klad-me/RK8266/pcb/ESP-01-LUT/mount/back.png

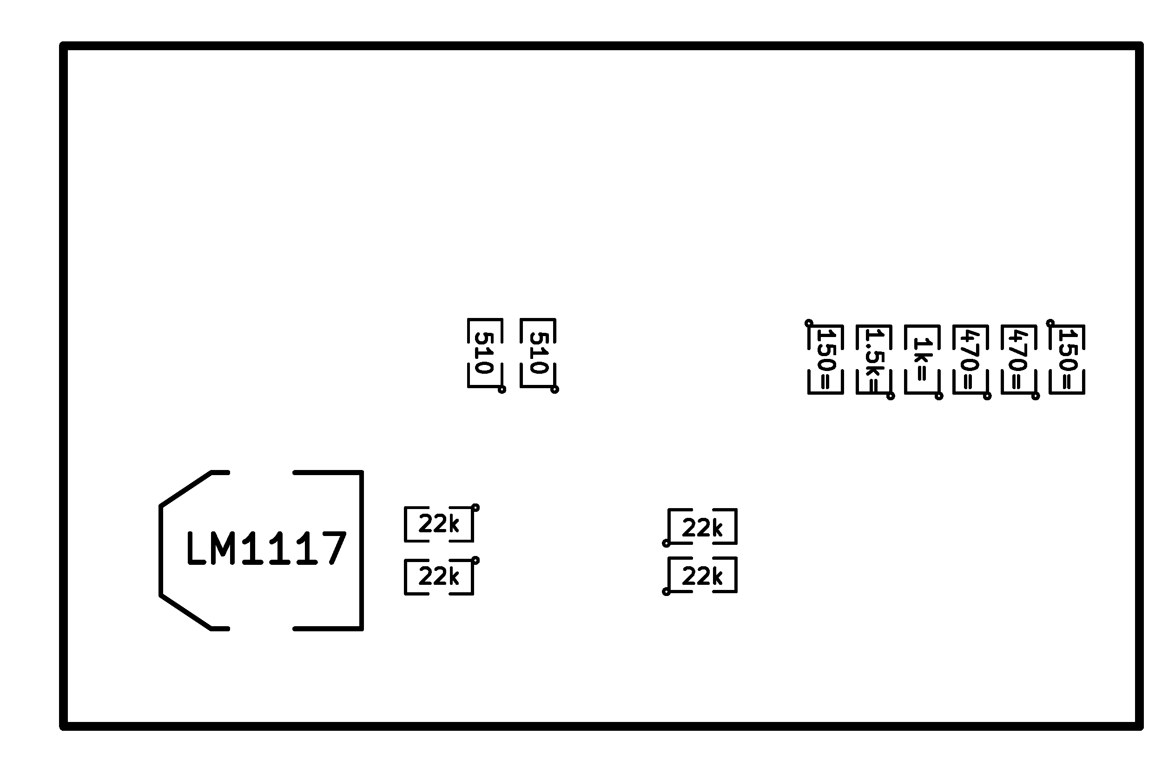
pcb/ESP-01-LUT/mount/back.png
