klad-me/RK8266/pcb/ESP-01-LUT/mount/front.png

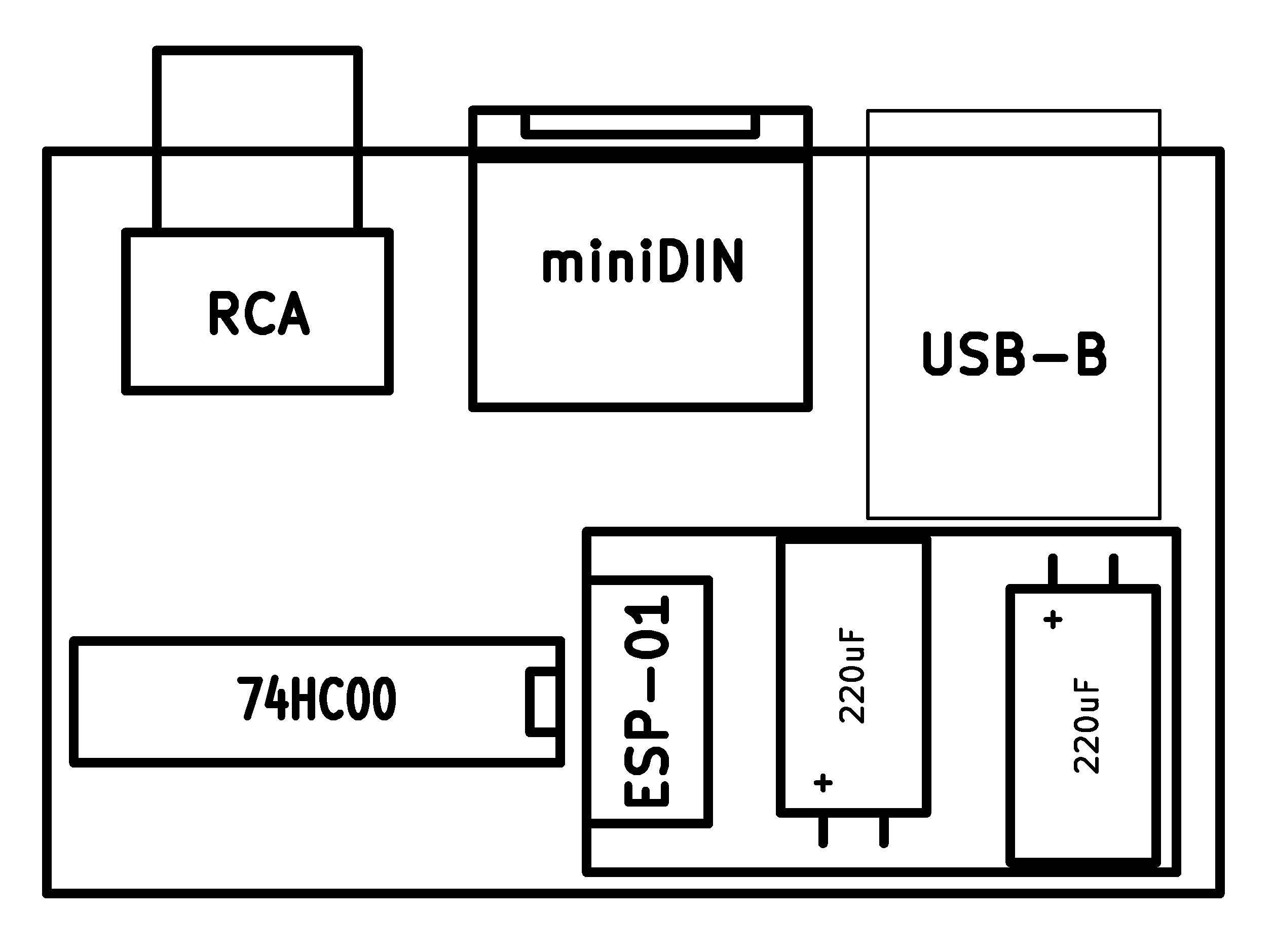
pcb/ESP-01-LUT/mount/front.png
