klad-me/RK8266/screenshots/rk8266_1.png

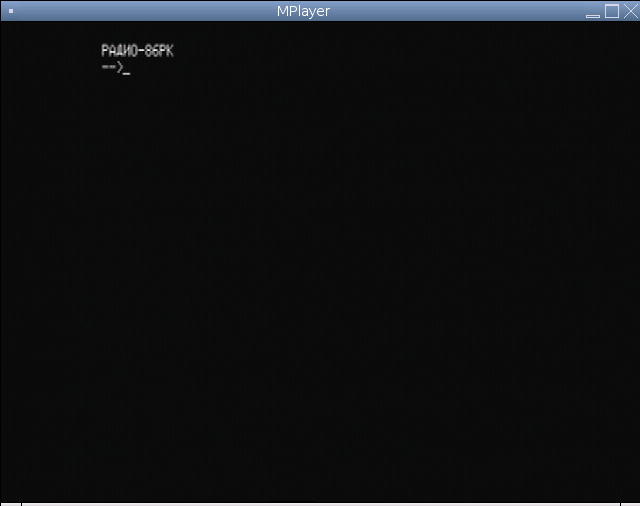
screenshots/rk8266_1.png
