klad-me/RK8266/screenshots/rk8266_3.png

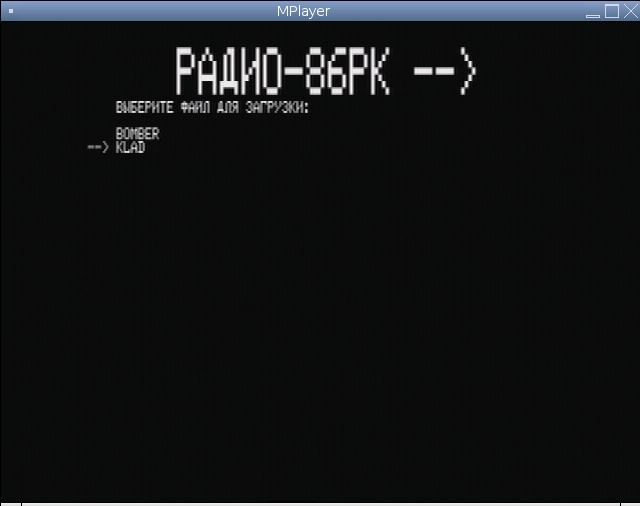
screenshots/rk8266_3.png
