klad-me/RK8266/screenshots/rk8266_4.png

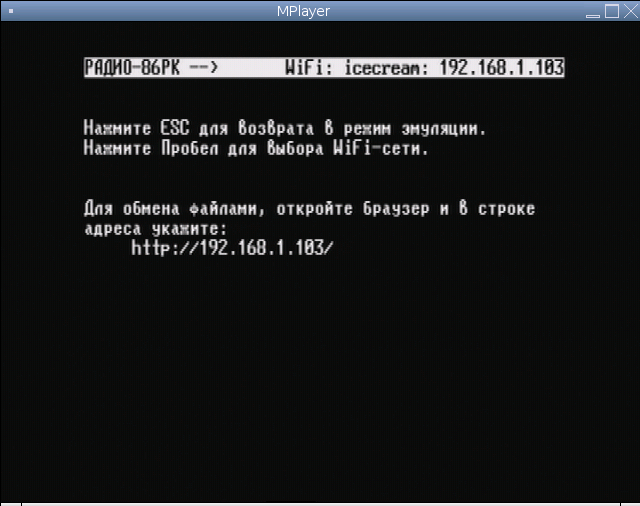
screenshots/rk8266_4.png
