klad-me/RK8266/screenshots/rk8266_5.png

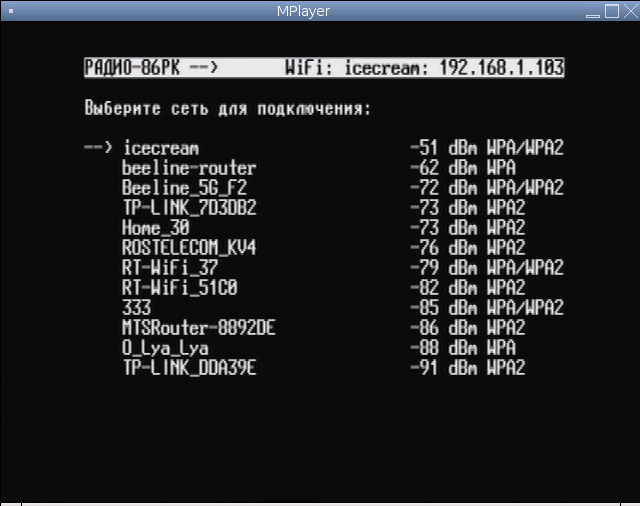
screenshots/rk8266_5.png
