klad-me/RK8266/screenshots/rk8266_7.png

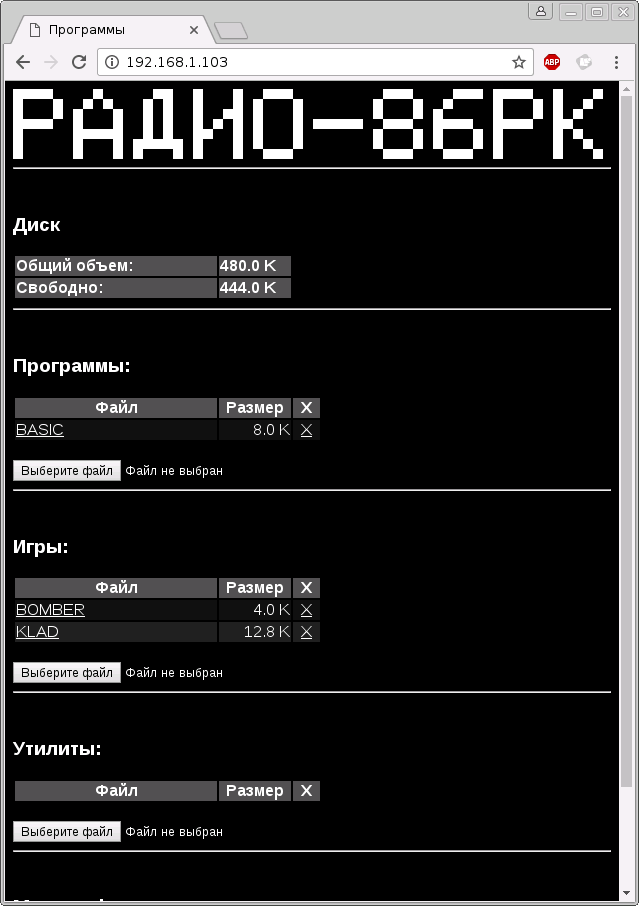
screenshots/rk8266_7.png
