klad-me/RK8266/pcb/ESP-01-LUT/RK86.sch

## KiCad design pcb/ESP-01-LUT/RK86.sch (2018-03-06)

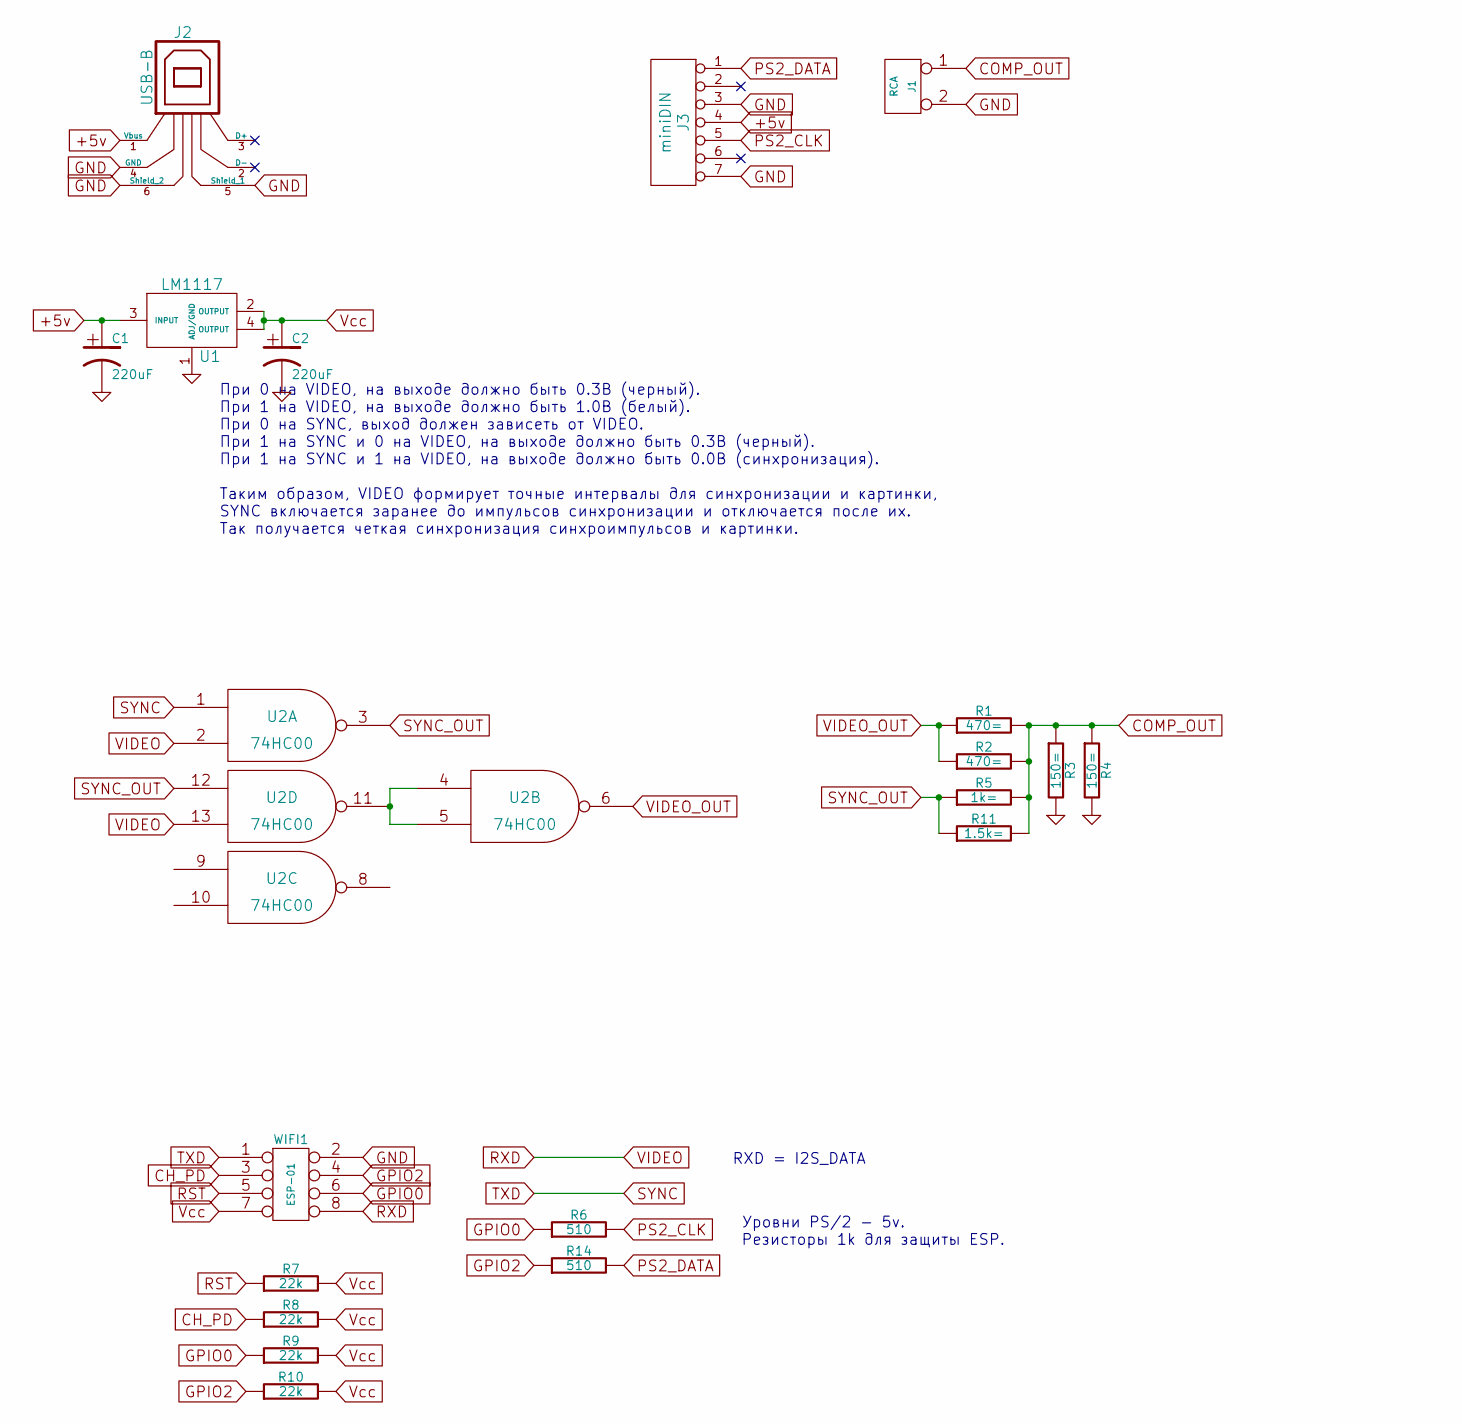
[picture p16: schematic RK86.sch]

Parts:
C1, C2: 220uF
J1: RCA
J2: USB-B
J3: miniDIN
R1, R2: 470=
R3, R4: 150=
R5: 1k=
R6, R14: 510
R7, R8, R9, R10: 22k
R11: 1.5k=
U1: LM1117
U2: 74HC00
WIFI1: ESP-01

Connections:
+5v: C1.1, J2.1 (Vbus), J3.4, U1.3 (INPUT)
CH_PD: R8.1, WIFI1.3
COMP_OUT: J1.1, R1.2, R2.2, R3.1, R4.1, R5.2, R11.2
GND: C1.2, C2.2, J1.2 (PM), J2.4 (GND), J2.5 (Shield_1), J2.6 (Shield_2), J3.3, J3.7, R3.2, R4.2, U1.1 (ADJ/GND), WIFI1.2
GPIO0: R6.1, R9.1, WIFI1.6
GPIO2: R10.1, R14.1, WIFI1.4
unnamed: U2.4, U2.5, U2.11
PS2_CLK: J3.5, R6.2
PS2_DATA: J3.1, R14.2
RST: R7.1, WIFI1.5
RXD: U2.2, U2.13, WIFI1.8
SYNC: U2.1, WIFI1.1
SYNC_OUT: R5.1, R11.1, U2.3, U2.12
VIDEO_OUT: R1.1, R2.1, U2.6
Vcc: C2.1, R7.2, R8.2, R9.2, R10.2, U1.2 (OUTPUT), U1.4 (OUTPUT), WIFI1.7

Notes on the sheet:
Уровни PS/2 - 5v. Резисторы 1k для защиты ESP.
RXD = I2S_DATA
При 0 на VIDEO, на выходе должно быть 0.3В (черный). При 1 на VIDEO, на выходе должно быть 1.0В (белый). При 0 на SYNC, выход должен зависеть от VIDEO. При 1 на SYNC и 0 на VIDEO, на выходе должно быть 0.3В (черный). При 1 на SYNC и 1 на VIDEO, на выходе должно быть 0.0В (синхронизация). Таким обра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
