klad-me/RK8266/soft/EmuAPP/src/rom.h

static const unsigned char AT_IRAM ROM_F800[] = {
  0xc3, 0x36, 0xf8, 0xc3, 0x63, 0xfe, 0xc3, 0x98, 0xfb, 0xc3, 0xba, 0xfc,
  0xc3, 0x46, 0xfc, 0xc3, 0xba, 0xfc, 0xc3, 0x01, 0xfe, 0xc3, 0xa5, 0xfc,
  0xc3, 0x22, 0xf9, 0xc3, 0x72, 0xfe, 0xc3, 0x7b, 0xfa, 0xc3, 0x7f, 0xfa,
  0xc3, 0xb6, 0xfa, 0xc3, 0x49, 0xfb, 0xc3, 0x16, 0xfb, 0xc3, 0xce, 0xfa,
  0xc3, 0x52, 0xff, 0xc3, 0x56, 0xff, 0x3e, 0x8a, 0x32, 0x03, 0x80, 0x31,
  0xcf, 0x76, 0xcd, 0xce, 0xfa, 0x21, 0x00, 0x76, 0x11, 0x5f, 0x76, 0x0e,
  0x00, 0xcd, 0xed, 0xf9, 0x21, 0xcf, 0x76, 0x22, 0x1c, 0x76, 0x21, 0x5a,
  0xff, 0xcd, 0x22, 0xf9, 0xcd, 0xce, 0xfa, 0x21, 0xff, 0x75, 0x22, 0x31,
  0x76, 0x21, 0x2a, 0x1d, 0x22, 0x2f, 0x76, 0x3e, 0xc3, 0x32, 0x26, 0x76,
  0x31, 0xcf, 0x76, 0x21, 0x66, 0xff, 0xcd, 0x22, 0xf9, 0x32, 0x02, 0x80,
  0x3d, 0x32, 0x02, 0xa0, 0xcd, 0xee, 0xf8, 0x21, 0x6c, 0xf8, 0xe5, 0x21,
  0x33, 0x76, 0x7e, 0xfe, 0x58, 0xca, 0xd3, 0xff, 0xfe, 0x55, 0xca, 0x00,
  0xf0, 0xf5, 0xcd, 0x2c, 0xf9, 0x2a, 0x2b, 0x76, 0x4d, 0x44, 0x2a, 0x29,
  0x76, 0xeb, 0x2a, 0x27, 0x76, 0xf1, 0xfe, 0x44, 0xca, 0xc5, 0xf9, 0xfe,
  0x43, 0xca, 0xd7, 0xf9, 0xfe, 0x46, 0xca, 0xed, 0xf9, 0xfe, 0x53, 0xca,
  0xf4, 0xf9, 0xfe, 0x54, 0xca, 0xff, 0xf9, 0xfe, 0x4d, 0xca, 0x26, 0xfa,
  0xfe, 0x47, 0xca, 0x3f, 0xfa, 0xfe, 0x49, 0xca, 0x86, 0xfa, 0xfe, 0x4f,
  0xca, 0x2d, 0xfb, 0xfe, 0x4c, 0xca, 0x08, 0xfa, 0xfe, 0x52, 0xca, 0x68,
  0xfa, 0xc3, 0x00, 0xf0, 0x3e, 0x33, 0xbd, 0xca, 0xf1, 0xf8, 0xe5, 0x21,
  0x9e, 0xff, 0xcd, 0x22, 0xf9, 0xe1, 0x2b, 0xc3, 0xf3, 0xf8, 0x21, 0x33,
  0x76, 0x06, 0x00, 0xcd, 0x63, 0xfe, 0xfe, 0x08, 0xca, 0xdc, 0xf8, 0xfe,
  0x7f, 0xca, 0xdc, 0xf8, 0xc4, 0xb9, 0xfc, 0x77, 0xfe, 0x0d, 0xca, 0x1a,
  0xf9, 0xfe, 0x2e, 0xca, 0x6c, 0xf8, 0x06, 0xff, 0x3e, 0x52, 0xbd, 0xca,
  0xae, 0xfa, 0x23, 0xc3, 0xf3, 0xf8, 0x78, 0x17, 0x11, 0x33, 0x76, 0x06,
  0x00, 0xc9, 0x7e, 0xa7, 0xc8, 0xcd, 0xb9, 0xfc, 0x23, 0xc3, 0x22, 0xf9,
  0x21, 0x27, 0x76, 0x11, 0x2d, 0x76, 0x0e, 0x00, 0xcd, 0xed, 0xf9, 0x11,
  0x34, 0x76, 0xcd, 0x5a, 0xf9, 0x22, 0x27, 0x76, 0x22, 0x29, 0x76, 0xd8,
  0x3e, 0xff, 0x32, 0x2d, 0x76, 0xcd, 0x5a, 0xf9, 0x22, 0x29, 0x76, 0xd8,
  0xcd, 0x5a, 0xf9, 0x22, 0x2b, 0x76, 0xd8, 0xc3, 0xae, 0xfa, 0x21, 0x00,
  0x00, 0x1a, 0x13, 0xfe, 0x0d, 0xca, 0x8e, 0xf9, 0xfe, 0x2c, 0xc8, 0xfe,
  0x20, 0xca, 0x5d, 0xf9, 0xd6, 0x30, 0xfa, 0xae, 0xfa, 0xfe, 0x0a, 0xfa,
  0x82, 0xf9, 0xfe, 0x11, 0xfa, 0xae, 0xfa, 0xfe, 0x17, 0xf2, 0xae, 0xfa,
  0xd6, 0x07, 0x4f, 0x29, 0x29, 0x29, 0x29, 0xda, 0xae, 0xfa, 0x09, 0xc3,
  0x5d, 0xf9, 0x37, 0xc9, 0x7c, 0xba, 0xc0, 0x7d, 0xbb, 0xc9, 0xcd, 0xa4,
  0xf9, 0xcd, 0x90, 0xf9, 0xc2, 0xa2, 0xf9, 0x33, 0x33, 0xc9, 0x23, 0xc9,
  0xcd, 0x72, 0xfe, 0xfe, 0x03, 0xc0, 0xcd, 0xce, 0xfa, 0xc3, 0xae, 0xfa,
  0xe5, 0x21, 0x6c, 0xff, 0xcd, 0x22, 0xf9, 0xe1, 0xc9, 0x7e, 0xc5, 0xcd,
  0xa5, 0xfc, 0x3e, 0x20, 0xcd, 0xb9, 0xfc, 0xc1, 0xc9, 0xcd, 0x78, 0xfb,
  0xcd, 0xb9, 0xf9, 0xcd, 0x96, 0xf9, 0x7d, 0xe6, 0x0f, 0xca, 0xc5, 0xf9,
  0xc3, 0xc8, 0xf9, 0x0a, 0xbe, 0xca, 0xe6, 0xf9, 0xcd, 0x78, 0xfb, 0xcd,
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
};
