klad-me/RK8266/soft/EmuAPP/src/zkg.c

#include "zkg.h"

#include "ets.h"


uint8_t zkg[4][1024];

const uint8_t AT_IRAM zkg_rom[1024]=
{
    // Line 0
    0x00, 0x38, 0x07, 0x3f, 0x00, 0x38, 0x07, 0x3f, 0x00, 0x0c, 0x00, 0x0c, 0x00, 0x00, 0x08, 0x0c, 
    0x00, 0x38, 0x07, 0x3f, 0x00, 0x38, 0x07, 0x3f, 0x00, 0x00, 0x00, 0x0c, 0x00, 0x04, 0x03, 0x00, 
    0x00, 0x04, 0x0a, 0x0a, 0x11, 0x18, 0x04, 0x06, 0x02, 0x08, 0x00, 0x00, 0x00, 0x00, 0x00, 0x00, 
    0x0e, 0x04, 0x0e, 0x1f, 0x02, 0x1f, 0x07, 0x1f, 0x0e, 0x0e, 0x00, 0x0c, 0x02, 0x00, 0x08, 0x0e, 
    0x0e, 0x04, 0x1e, 0x0e, 0x1e, 0x1f, 0x1f, 0x0e, 0x11, 0x0e, 0x01, 0x11, 0x10, 0x11, 0x11, 0x0e, 
    0x1e, 0x0e, 0x1e, 0x0e, 0x1f, 0x11, 0x11, 0x11, 0x11, 0x11, 0x1f, 0x0e, 0x00, 0x0e, 0x0e, 0x00, 
    0x12, 0x04, 0x1f, 0x12, 0x06, 0x1f, 0x04, 0x1f, 0x11, 0x11, 0x15, 0x11, 0x07, 0x11, 0x11, 0x0e, 
    0x1f, 0x0f, 0x1e, 0x0e, 0x1f, 0x11, 0x11, 0x1e, 0x10, 0x11, 0x0e, 0x11, 0x0e, 0x15, 0x11, 0x3f, 
    // Line 1
    0x00, 0x38, 0x07, 0x3f, 0x00, 0x38, 0x07, 0x3f, 0x00, 0x0c, 0x00, 0x1e, 0x00, 0x00, 0x0c, 0x0c, 
    0x00, 0x38, 0x07, 0x3f, 0x00, 0x38, 0x07, 0x3f, 0x00, 0x00, 0x00, 0x0c, 0x00, 0x0c, 0x04, 0x00, 
    0x00, 0x04, 0x0a, 0x0a, 0x0e, 0x19, 0x0a, 0x06, 0x04, 0x04, 0x04, 0x04, 0x00, 0x00, 0x00, 0x01, 
    0x11, 0x0c, 0x11, 0x01, 0x06, 0x10, 0x08, 0x01, 0x11, 0x11, 0x0c, 0x0c, 0x04, 0x00, 0x04, 0x11, 
    0x11, 0x0a, 0x11, 0x11, 0x09, 0x10, 0x10, 0x11, 0x11, 0x04, 0x01, 0x12, 0x10, 0x1b, 0x11, 0x11, 
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
    0x11, 0x11, 0x10, 0x0e, 0x04, 0x10, 0x11, 0x1e, 0x1e, 0x19, 0x0e, 0x1f, 0x0e, 0x01, 0x00, 0x3f, 
    // Line 7
    0x00, 0x00, 0x00, 0x00, 0x07, 0x07, 0x07, 0x07, 0x00, 0x21, 0x00, 0x0c, 0x00, 0x00, 0x08, 0x0c, 
    0x38, 0x38, 0x38, 0x38, 0x3f, 0x3f, 0x3f, 0x3f, 0x00, 0x00, 0x00, 0x0c, 0x00, 0x04, 0x0c, 0x00, 
    0x00, 0x00, 0x00, 0x00, 0x00, 0x00, 0x00, 0x00, 0x00, 0x00, 0x00, 0x00, 0x00, 0x00, 0x00, 0x00, 
    0x00, 0x00, 0x00, 0x00, 0x00, 0x00, 0x00, 0x00, 0x00, 0x00, 0x00, 0x00, 0x00, 0x00, 0x00, 0x00, 
    0x00, 0x00, 0x00, 0x00, 0x00, 0x00, 0x00, 0x00, 0x00, 0x00, 0x00, 0x00, 0x00, 0x00, 0x00, 0x00, 
    0x00, 0x00, 0x00, 0x00, 0x00, 0x00, 0x00, 0x00, 0x00, 0x00, 0x00, 0x00, 0x00, 0x00, 0x00, 0x00, 
    0x00, 0x00, 0x00, 0x00, 0x00, 0x00, 0x00, 0x00, 0x00, 0x00, 0x00, 0x00, 0x00, 0x00, 0x00, 0x00, 
    0x00, 0x00, 0x00, 0x00, 0x00, 0x00, 0x00, 0x00, 0x00, 0x00, 0x00, 0x00, 0x00, 0x00, 0x3f, 0x00, 
};
