klad-me/RK8266/soft/EmuAPP/src/tv.h

#ifndef TV_H
#define TV_H


#include "ets.h"


#ifdef __cplusplus
extern "C" {
#endif


extern uint8_t tv_empty_line[64];


void tv_init(void);
void tv_start(void);


#ifdef __cplusplus
}
#endif


#endif
