klad-me/RK8266/soft/EmuAPP/src/align4.h

#ifndef ALIGN4_H
#define ALIGN4_H


#include <inttypes.h>


#ifdef __cplusplus
extern "C" {
#endif


uint8_t  r_u8(const uint8_t *addr);
uint16_t r_u16(const uint16_t *addr);


#ifdef __cplusplus
}
#endif


#endif
