klad-me/RK8266/soft/boot-2apps/src/ram_loader.h

const uint32_t entry_addr = 0x4010fcd4;

const uint32_t _text_addr = 0x4010fc00;
const uint32_t _text_len = 224;
const uint8_t  _text_data[] = {
  0x00, 0x00, 0x00, 0x00, 0x00, 0x00, 0x00, 0x00, 0x00, 0x00, 0x00, 0x00, 0x00, 0x00, 0x00, 0x00,
  0x00, 0x00, 0x00, 0x00, 0x00, 0x00, 0x00, 0x00, 0x00, 0x00, 0x00, 0x00, 0x00, 0x00, 0x00, 0x00,
  0x00, 0x00, 0x00, 0x00, 0x00, 0x00, 0x00, 0x00, 0x00, 0x00, 0x00, 0x00, 0x00, 0x00, 0x00, 0x00,
  0x1c, 0x4b, 0x00, 0x40, 0xb4, 0x18, 0x00, 0x40, 0x92, 0xa1, 0x30, 0x90, 0x11, 0xc0, 0x0c, 0x84,
  0x3d, 0x01, 0xc2, 0x61, 0x4a, 0x02, 0x61, 0x4b, 0xcd, 0x02, 0xd2, 0x61, 0x49, 0xe2, 0x61, 0x48,
  0xf2, 0x61, 0x47, 0x01, 0xf7, 0xff, 0xc0, 0x00, 0x00, 0x22, 0x01, 0x01, 0x48, 0x11, 0x22, 0x61,
  0x40, 0x42, 0x61, 0x41, 0x8b, 0xcc, 0x16, 0xe2, 0x04, 0x2d, 0x0c, 0x3d, 0x01, 0x0c, 0x84, 0x01,
  0xf0, 0xff, 0xc0, 0x00, 0x00, 0xf8, 0x11, 0x8b, 0xcc, 0xd8, 0x01, 0xac, 0xbf, 0x42, 0xa1, 0x00,
  0x2d, 0x0c, 0x3d, 0x01, 0xed, 0x0f, 0xf7, 0xb4, 0x02, 0x40, 0xe4, 0x20, 0x4d, 0x0e, 0x01, 0xe8,
  0xff, 0xc0, 0x00, 0x00, 0x2d, 0x0d, 0x3d, 0x01, 0x4d, 0x0e, 0xe0, 0xff, 0xc0, 0xea, 0xcc, 0x01,
  0xe5, 0xff, 0xc0, 0x00, 0x00, 0xea, 0xdd, 0x56, 0x2f, 0xfd, 0x22, 0x21, 0x40, 0x0b, 0xf2, 0xf0,
  0x40, 0x74, 0x42, 0x61, 0x40, 0x56, 0x04, 0xfb, 0x02, 0x21, 0x4b, 0x92, 0xa1, 0x30, 0x22, 0x21,
  0x41, 0xc2, 0x21, 0x4a, 0xd2, 0x21, 0x49, 0xe2, 0x21, 0x48, 0xf2, 0x21, 0x47, 0x9a, 0x11, 0x0d,
  0xf0, 0x00, 0x00, 0x00, 0xfd, 0x00, 0x05, 0xf6, 0xff, 0x0d, 0x0f, 0xa0, 0x02, 0x00, 0x0d, 0xf0,
};
